lorenzonotaro/lncpu/v1/kicad/v1.kicad_pcb

## KiCad design v1/kicad/v1.kicad_pcb (2025-12-29)

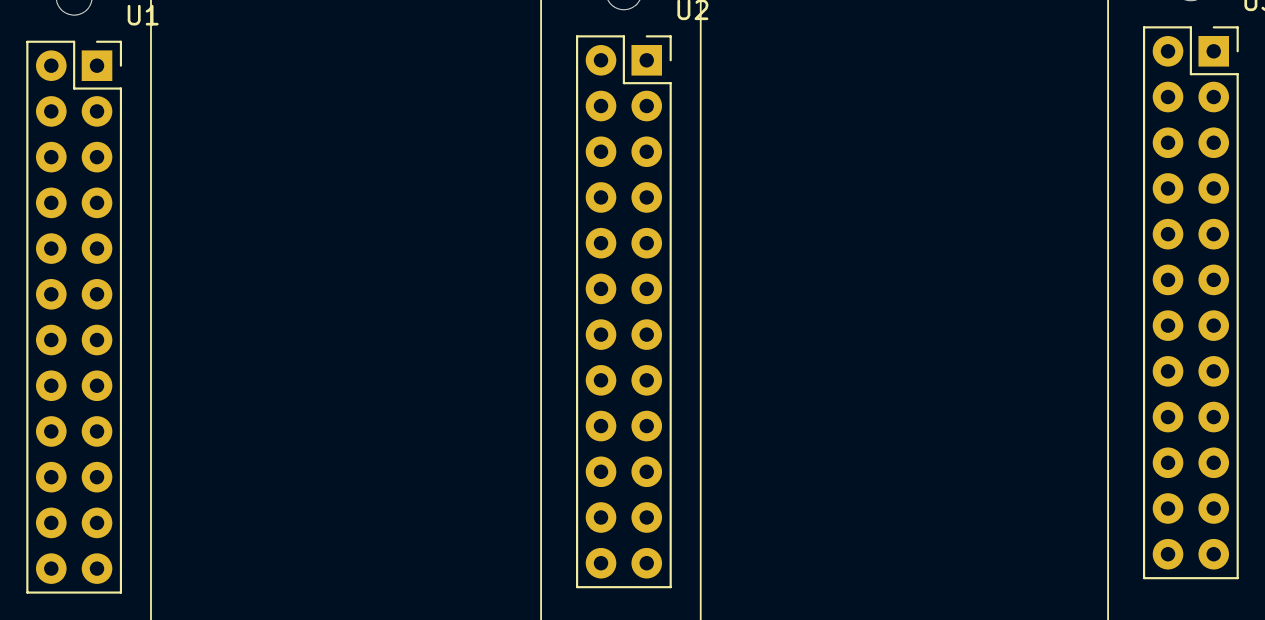
[picture p31: board v1.kicad_pcb from above]

Board: 2 copper layers, 3 parts (0 on the bottom side), 12 nets, no tracks yet.

Parts:
U1: RB; LNCPU_GP_Register
U2: RC; LNCPU_GP_Register
U3: RD; LNCPU_GP_Register

Connections:
DBUS0: U1.4 (DBUS_{0}), U2.4 (DBUS_{0}), U3.4 (DBUS_{0})
DBUS1: U1.6 (DBUS_{1}), U2.6 (DBUS_{1}), U3.6 (DBUS_{1})
DBUS2: U1.8 (DBUS_{2}), U2.8 (DBUS_{2}), U3.8 (DBUS_{2})
DBUS3: U1.10 (DBUS_{3}), U2.10 (DBUS_{3}), U3.10 (DBUS_{3})
DBUS4: U1.12 (DBUS_{4}), U2.12 (DBUS_{4}), U3.12 (DBUS_{4})
DBUS5: U1.14 (DBUS_{5}), U2.14 (DBUS_{5}), U3.14 (DBUS_{5})
DBUS6: U1.16 (DBUS_{6}), U2.16 (DBUS_{6}), U3.16 (DBUS_{6})
DBUS7: U1.18 (DBUS_{7}), U2.18 (DBUS_{7}), U3.18 (DBUS_{7})
GND: U1.1 (GND), U1.17 (GND), U1.20 (GND), U1.22 (GND), U2.1 (GND), U2.17 (GND), U2.20 (GND), U2.22 (GND), U3.1 (GND), U3.17 (GND), U3.20 (GND), U3.22 (GND)
PHI_{2}: U1.3 (~R_{en}), U2.3 (~R_{en}), U3.3 (~R_{en})
RST: U1.19 (RST), U2.19 (RST), U3.19 (RST)
VCC: U1.2 (VCC), U1.24 (VCC), U2.2 (VCC), U2.24 (VCC), U3.2 (VCC), U3.24 (VCC)
