lorenzonotaro/lncpu/eeprom-serial-loader/loaders/AT28C64B/AT28C64B-circuit/AT28C64B-circuit.kicad_pcb

## KiCad design eeprom-serial-loader/loaders/AT28C64B/AT28C64B-circuit/AT28C64B-circuit.kicad_pcb (2024-08-27)

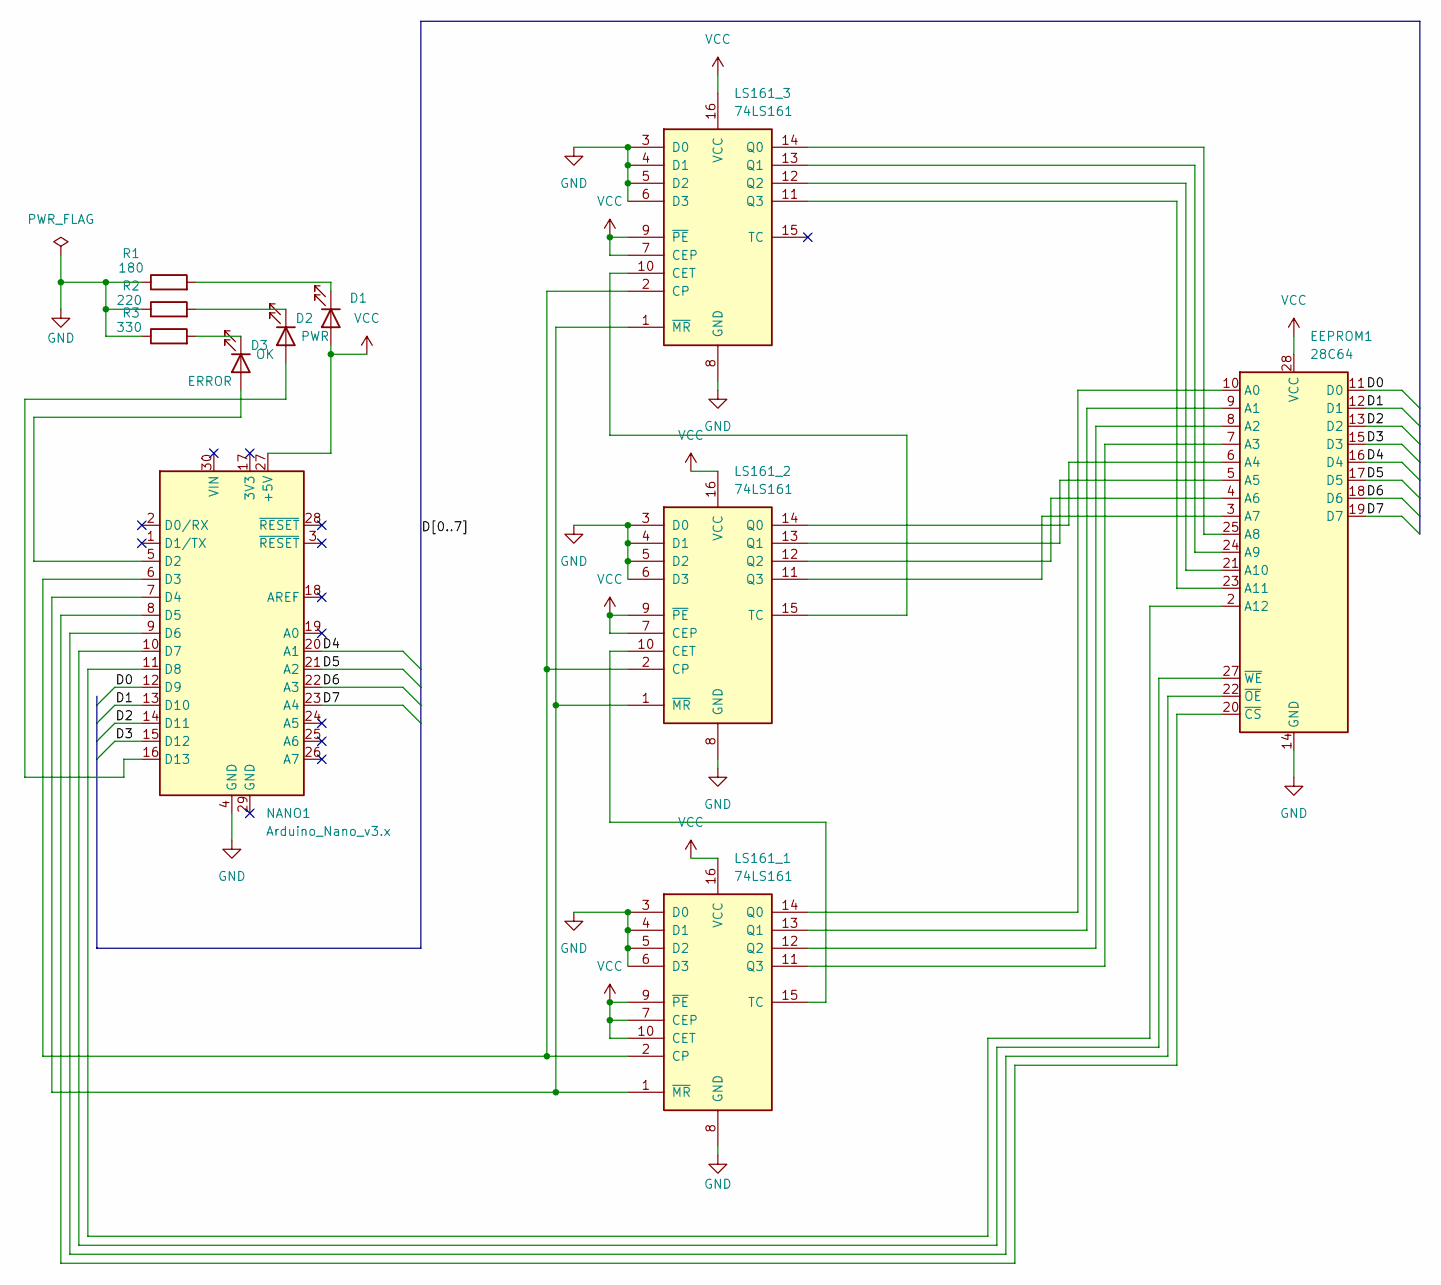
[picture p32: schematic AT28C64B-circuit.kicad_sch]

Parts:
D1: PWR; LED_D3.0mm
D2: OK; LED_D3.0mm
D3: ERROR; LED_D3.0mm
EEPROM1: 28C64; DIP-28_W15.24mm_Socket_LongPads
LS161_1, LS161_2, LS161_3: 74LS161; DIP-16_W7.62mm
NANO1: Arduino_Nano_v3.x; Arduino_Nano
R1: 180; R_Axial_DIN0207_L6.3mm_D2.5mm_P10.16mm_Horizontal
R2: 220; R_Axial_DIN0207_L6.3mm_D2.5mm_P10.16mm_Horizontal
R3: 330; R_Axial_DIN0207_L6.3mm_D2.5mm_P10.16mm_Horizontal

Connections:
/D0: EEPROM1.11 (D0), NANO1.12 (D9)
/D1: EEPROM1.12 (D1), NANO1.13 (D10)
/D2: EEPROM1.13 (D2), NANO1.14 (D11)
/D3: EEPROM1.15 (D3), NANO1.15 (D12)
/D4: EEPROM1.16 (D4), NANO1.20 (A1)
/D5: EEPROM1.17 (D5), NANO1.21 (A2)
/D6: EEPROM1.18 (D6), NANO1.22 (A3)
/D7: EEPROM1.19 (D7), NANO1.23 (A4)
GND: EEPROM1.14 (GND), LS161_1.3 (D0), LS161_1.4 (D1), LS161_1.5 (D2), LS161_1.6 (D3), LS161_1.8 (GND), LS161_2.3 (D0), LS161_2.4 (D1), LS161_2.5 (D2), LS161_2.6 (D3), LS161_2.8 (GND), LS161_3.3 (D0), LS161_3.4 (D1), LS161_3.5 (D2), LS161_3.6 (D3), LS161_3.8 (GND), NANO1.4 (GND), R1.1, R2.1, R3.1
unnamed: D1.1 (K), R1.2
unnamed: D2.2 (A), NANO1.16 (D13)
unnamed: D2.1 (K), R2.2
unnamed: D3.2 (A), NANO1.5 (D2)
unnamed: D3.1 (K), R3.2
unnamed: EEPROM1.10 (A0), LS161_1.14 (Q0)
unnamed: EEPROM1.9 (A1), LS161_1.13 (Q1)
unnamed: EEPROM1.8 (A2), LS161_1.12 (Q2)
unnamed: EEPROM1.7 (A3), LS161_1.11 (Q3)
unnamed: EEPROM1.6 (A4), LS161_2.14 (Q0)
unnamed: EEPROM1.5 (A5), LS161_2.13 (Q1)
unnamed: EEPROM1.4 (A6), LS161_2.12 (Q2)
unnamed: EEPROM1.3 (A7), LS161_2.11 (Q3)
unnamed: EEPROM1.25 (A8), LS161_3.14 (Q0)
unnamed: EEPROM1.24 (A9), LS161_3.13 (Q1)
unnamed: EEPROM1.21 (A10), LS161_3.12 (Q2)
unnamed: EEPROM1.23 (A11), LS161_3.11 (Q3)
unnamed: EEPROM1.2 (A12), NANO1.11 (D8)
unnamed: EEPROM1.20 (~CS), NANO1.8 (D5)
unnamed: EEPROM1.22 (~OE), NANO1.9 (D6)
unnamed: EEPROM1.27 (~WE), NANO1.10 (D7)
unnamed: LS161_1.2 (CP), LS161_2.2 (CP), LS161_3.2 (CP), NANO1.6 (D3)
unnamed: LS161_1.15 (TC), LS161_2.10 (CET)
unnamed: LS161_1.1 (~MR), LS161_2.1 (~MR), LS161_3.1 (~MR), NANO1.7 (D4)
unnamed: LS161_2.15 (TC), LS161_3.10 (CET)
VCC: D1.2 (A), EEPROM1.28 (VCC), LS161_1.7 (CEP), LS161_1.9 (~PE), LS161_1.10 (CET), LS161_1.16 (VCC), LS161_2.7 (CEP), LS161_2.9 (~PE), LS161_2.16 (VCC), LS161_3.7 (CEP), LS161_3.9 (~PE), LS161_3.16 (VCC), NANO1.27 (+5V)

Board: 2 copper layers, 11 parts (0 on the bottom side), 35 nets, no tracks yet.
