lorenzonotaro/lncpu/v1/kicad/alu/alu/alu-base.kicad_pcb

## KiCad design v1/kicad/alu/alu/alu-base.kicad_pcb (2026-03-26)

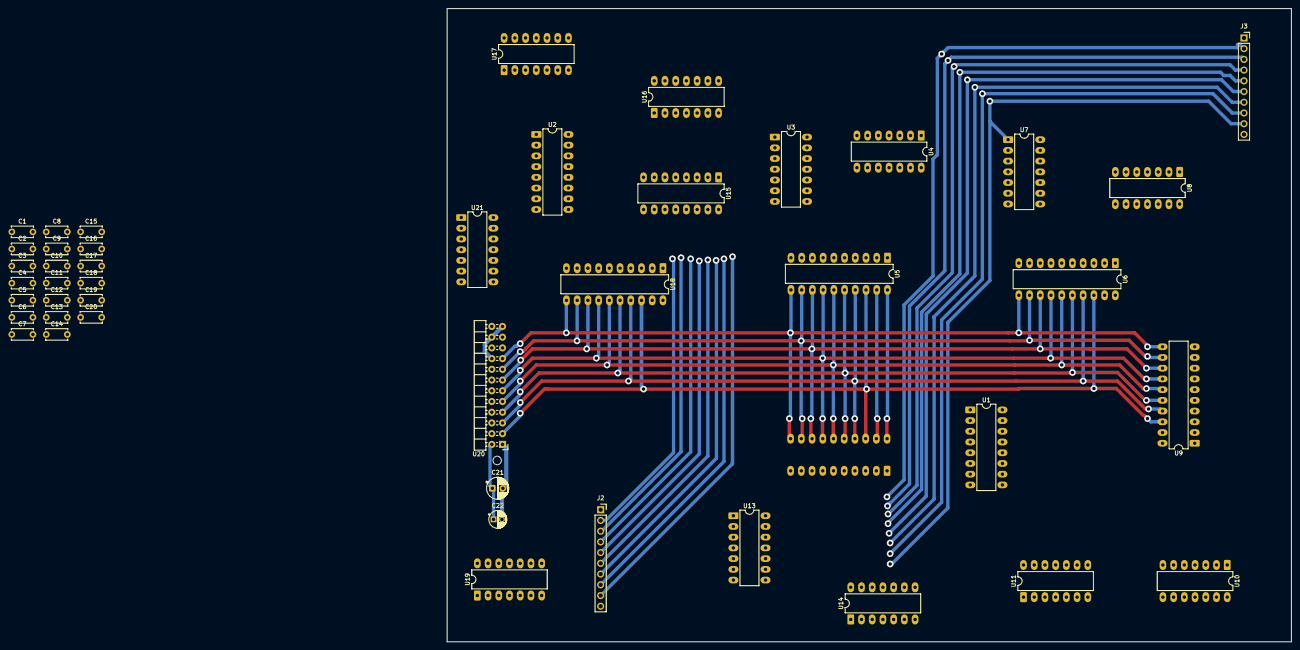
[picture p33: board alu-base.kicad_pcb from above]

Board: 2 copper layers, 200.0 x 150.0 mm, 45 parts (1 on the bottom side), 92 nets.

Parts:
C1, C2, C3, C4, C5, C6, C7, C8, C9, C10, C11, C12, C13, C14, C15: 100n; C_Disc_D5.0mm_W2.5mm_P5.00mm
C16, C17, C18, C19, C20: 220n; C_Disc_D5.0mm_W2.5mm_P5.00mm
C21: 47uF; CP_Radial_D5.0mm_P2.50mm
C22: 1uF; CP_Radial_D4.0mm_P2.00mm-Large-Holes
J2: X_{in}; PinSocket_1x10_P2.54mm_Vertical
J3: Y_{in}; PinSocket_1x10_P2.54mm_Vertical
U1: 74LS138; DIP-16_W7.62mm_LongPads
U2, U15: 74LS283; DIP-16_W7.62mm_LongPads
U3, U4: 74LS32; DIP-14_W7.62mm_LongPads
U5, U6, U9, U12, U18: 74HCT541; DIP-20_W7.62mm_LongPads
U7, U8, U19: 74LS08; DIP-14_W7.62mm_LongPads
U10, U11, U16, U17, U21: 74LS86; DIP-14_W7.62mm_LongPads
U13, U14: 74LS04; DIP-14_W7.62mm_LongPads
U20: LNCPU Type B Header; LNCPU_Type_B_Header

Connections:
/D0: U5.18 (Y0), U6.18 (Y0), U9.18 (Y0), U12.18 (Y0), U18.18 (Y0), U20.3 (DBUS_{0})
/D1: U5.17 (Y1), U6.17 (Y1), U9.17 (Y1), U12.17 (Y1), U18.17 (Y1), U20.5 (DBUS_{1})
/D2: U5.16 (Y2), U6.16 (Y2), U9.16 (Y2), U12.16 (Y2), U18.16 (Y2), U20.7 (DBUS_{2})
/D3: U5.15 (Y3), U6.15 (Y3), U9.15 (Y3), U12.15 (Y3), U18.15 (Y3), U20.9 (DBUS_{3})
/D4: U5.14 (Y4), U6.14 (Y4), U9.14 (Y4), U12.14 (Y4), U18.14 (Y4), U20.11 (DBUS_{4})
/D5: U5.13 (Y5), U6.13 (Y5), U9.13 (Y5), U12.13 (Y5), U18.13 (Y5), U20.13 (DBUS_{5})
/D6: U5.12 (Y6), U6.12 (Y6), U9.12 (Y6), U12.12 (Y6), U18.12 (Y6), U20.15 (DBUS_{6})
/D7: U5.11 (Y7), U6.11 (Y7), U9.11 (Y7), U12.11 (Y7), U18.11 (Y7), U20.17 (DBUS_{7})
/X0: J2.2 (D0), U4.13, U8.13, U11.13, U14.3, U15.5 (A1)
/X1: J2.3 (D1), U3.13, U7.13, U10.13, U14.1, U15.3 (A2)
/X2: J2.4 (D2), U4.10, U8.10, U11.10, U13.13, U15.14 (A3)
/X3: J2.5 (D3), U3.10, U7.10, U10.10, U13.11, U15.12 (A4)
/X4: J2.6 (D4), U2.5 (A1), U4.5, U8.5, U11.5, U13.9
/X5: J2.7 (D5), U2.3 (A2), U3.5, U7.5, U10.5, U13.5
/X6: J2.8 (D6), U2.14 (A3), U4.2, U8.2, U11.2, U13.3
/X7: J2.9 (D7), U2.12 (A4), U3.2, U7.2, U10.2, U13.1
/Y0: J3.2 (D0), U4.12, U8.12, U11.12, U17.13
/Y1: J3.3 (D1), U3.12, U7.12, U10.12, U16.13
/Y2: J3.4 (D2), U4.9, U8.9, U11.9, U17.10
/Y3: J3.5 (D3), U3.9, U7.9, U10.9, U16.10
/Y4: J3.6 (D4), U4.4, U8.4, U11.4, U17.5
/Y5: J3.7 (D5), U3.4, U7.4, U10.4, U16.5
/Y6: J3.8 (D6), U4.1, U8.1, U11.1, U17.2
/Y7: J3.9 (D7), U3.1, U7.1, U10.1, U16.2
/Y_{xor}EN2_{0}: U15.6 (B1), U17.11
/Y_{xor}EN2_{1}: U15.2 (B2), U16.11
/Y_{xor}EN2_{2}: U15.15 (B3), U17.8
/Y_{xor}EN2_{3}: U15.11 (B4), U16.8
/Y_{xor}EN2_{4}: U2.6 (B1), U17.6
/Y_{xor}EN2_{5}: U2.2 (B2), U16.6
/Y_{xor}EN2_{6}: U2.15 (B3), U17.3
/Y_{xor}EN2_{7}: U2.11 (B4), U16.3
/~EN1: U1.14 (O1), U19.5
/~EN2: U1.13 (O2), U14.5, U19.4
/~EN3: U1.12 (O3), U5.1 (G1)
/~EN4: U1.11 (O4), U6.1 (G1)
/~EN5: U1.10 (O5), U9.1 (G1)
/~EN6: U1.9 (O6), U12.1 (G1)
C_{out}: U19.3, U20.14 (CTRL_{5})
GND: C1.2, C2.1, C3.1, C4.1, C5.1, C6.1, C7.1, C8.1, C9.1, C10.1, C11.1, C12.1, C13.1, C14.2, C15.2, C16.2, C17.2, C18.2, C19.2, C20.2, C21.2, C22.2, J2.1 (GND), J2.10 (GND), J3.1 (GND), J3.10 (GND), U1.8 (GND), U2.8 (GND), U3.7 (GND), U4.7 (GND), U5.10 (GND), U6.10 (GND), U7.7 (GND), U8.7 (GND), U9.10 (GND), U10.7 (GND), U11.7 (GND), U12.10 (GND), U13.7 (GND), U14.7 (GND), U14.11, U14.13, U15.8 (GND), U16.7 (GND), U17.7 (GND), U18.10 (GND), U19.7 (GND), U19.9, U19.10, U19.12, U19.13, U20.1 (GND), U20.18 (GND), U20.22 (GND), U20.23 (GND), U21.4, U21.5, U21.7 (GND), U21.9, U21.10, U21.12, U21.13
unnamed: U1.1 (A0), U20.12 (CTRL_{4})
unnamed: U1.2 (A1), U20.10 (CTRL_{3})
unnamed: U1.3 (A2), U20.8 (CTRL_{2})
unnamed: U1.4 (E1), U20.4 (CTRL_{0})
unnamed: U2.9 (C4), U21.2
unnamed: U4.11, U5.2 (A0)
unnamed: U3.11, U5.3 (A1)
unnamed: U4.8, U5.4 (A2)
unnamed: U3.8, U5.5 (A3)
unnamed: U4.6, U5.6 (A4)
unnamed: U3.6, U5.7 (A5)
unnamed: U4.3, U5.8 (A6)
unnamed: U3.3, U5.9 (A7)
unnamed: U6.2 (A0), U8.11
unnamed: U6.3 (A1), U7.11
unnamed: U6.4 (A2), U8.8
unnamed: U6.5 (A3), U7.8
unnamed: U6.6 (A4), U8.6
unnamed: U6.7 (A5), U7.6
unnamed: U6.8 (A6), U8.3
unnamed: U6.9 (A7), U7.3
unnamed: U9.2 (A0), U11.11
unnamed: U9.3 (A1), U10.11
unnamed: U9.4 (A2), U11.8
unnamed: U9.5 (A3), U10.8
unnamed: U9.6 (A4), U11.6
unnamed: U9.7 (A5), U10.6
unnamed: U9.8 (A6), U11.3
unnamed: U9.9 (A7), U10.3
unnamed: U12.2 (A0), U14.4
unnamed: U12.3 (A1), U14.2
unnamed: U12.4 (A2), U13.12
unnamed: U12.5 (A3), U13.10
unnamed: U12.6 (A4), U13.8
unnamed: U12.7 (A5), U13.6
unnamed: U12.8 (A6), U13.4
unnamed: U12.9 (A7), U13.2
unnamed: U14.8, U19.2
unnamed: U14.6, U15.7 (C0), U16.1, U16.4, U16.9, U16.12, U17.1, U17.4, U17.9, U17.12, U21.1
unnamed: U2.7 (C0), U15.9 (C4)
unnamed: U15.4 (S1), U18.2 (A0)
unnamed: U15.1 (S2), U18.3 (A1)
unnamed: U15.13 (S3), U18.4 (A2)
unnamed: U15.10 (S4), U18.5 (A3)
unnamed: U2.4 (S1), U18.6 (A4)
unnamed: U2.1 (S2), U18.7 (A5)
unnamed: U2.13 (S3), U18.8 (A6)
unnamed: U2.10 (S4), U18.9 (A7)
unnamed: U14.9, U18.1 (G1), U19.6
unnamed: U19.1, U21.3
VCC: C1.1, C2.2, C3.2, C4.2, C5.2, C6.2, C7.2, C8.2, C9.2, C10.2, C11.2, C12.2, C13.2, C14.1, C15.1, C16.1, C17.1, C18.1, C19.1, C20.1, C21.1, C22.1, U1.6 (E3), U1.16 (VCC), U2.16 (VCC), U3.14 (VCC), U4.14 (VCC), U5.20 (VCC), U6.20 (VCC), U7.14 (VCC), U8.14 (VCC), U9.20 (VCC), U10.14 (VCC), U11.14 (VCC), U12.20 (VCC), U13.14 (VCC), U14.14 (VCC), U15.16 (VCC), U16.14 (VCC), U17.14 (VCC), U18.20 (VCC), U19.14 (VCC), U20.2 (VCC), U20.24 (VCC), U21.14 (VCC)
~ALU_{out}: U1.5 (E2), U5.19 (G2), U6.19 (G2), U9.19 (G2), U12.19 (G2), U18.19 (G2), U20.6 (CTRL_{1})
